Tonikiller10000/W65C02Computer/ComputerPics/20220521_232128.jpg

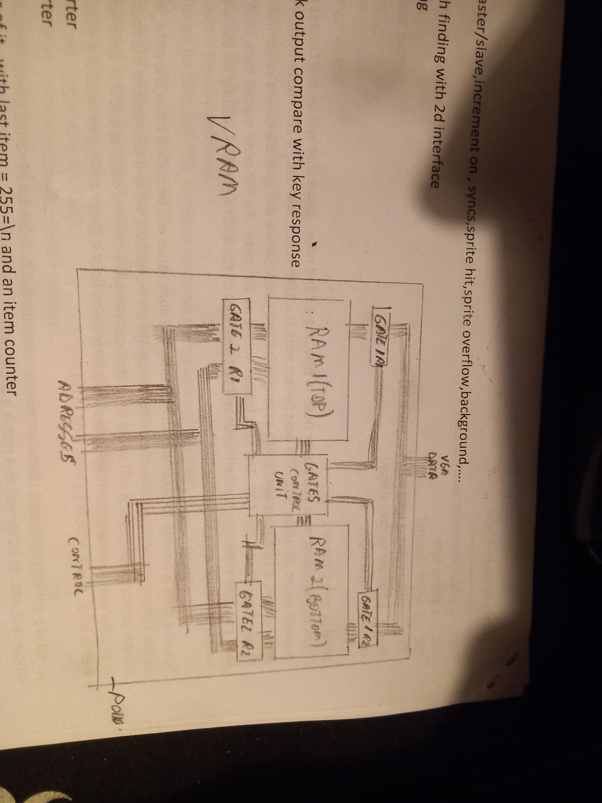
ComputerPics/20220521_232128.jpg
