Tonikiller10000/W65C02Computer/ComputerPics/20220714_215615.jpg

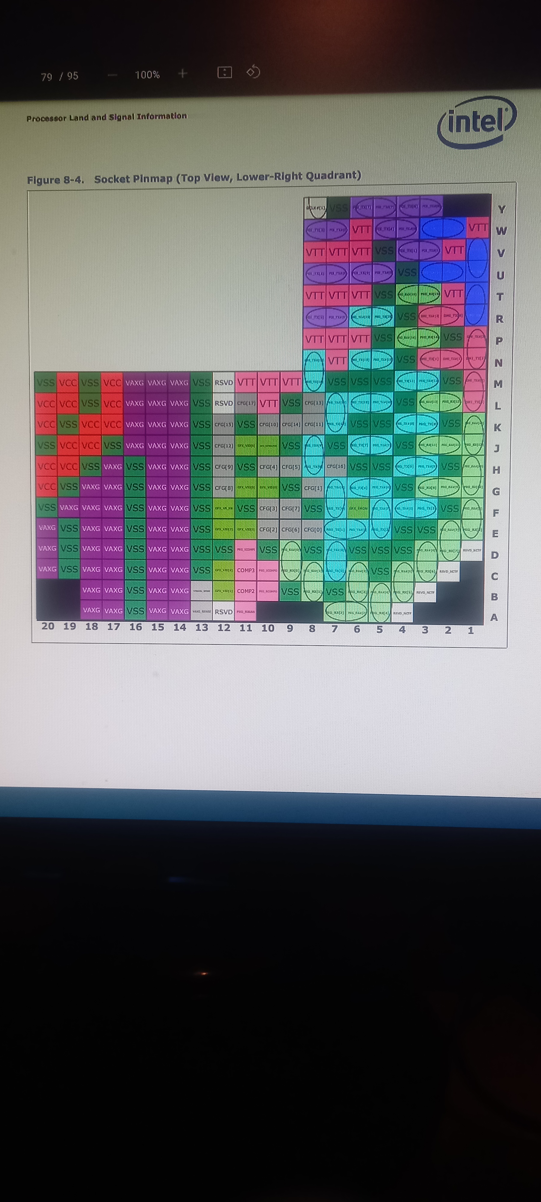
ComputerPics/20220714_215615.jpg
