Tonikiller10000/W65C02Computer/ComputerPics/20230511_115035.jpg

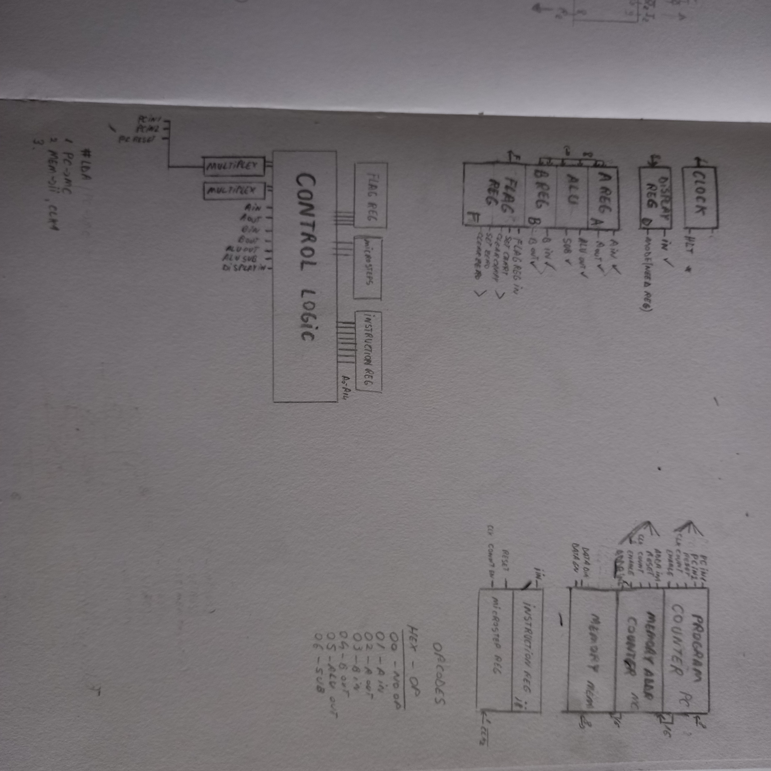
ComputerPics/20230511_115035.jpg
