Tonikiller10000/W65C02Computer/ComputerPics/20230919_042227.jpg

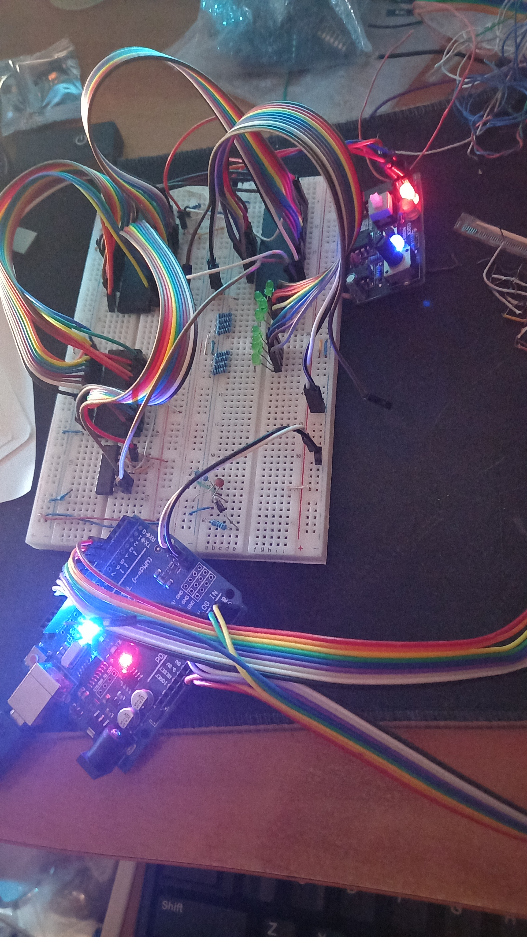
ComputerPics/20230919_042227.jpg
