Tonikiller10000/W65C02Computer/ComputerPics/20240304_115058.jpg

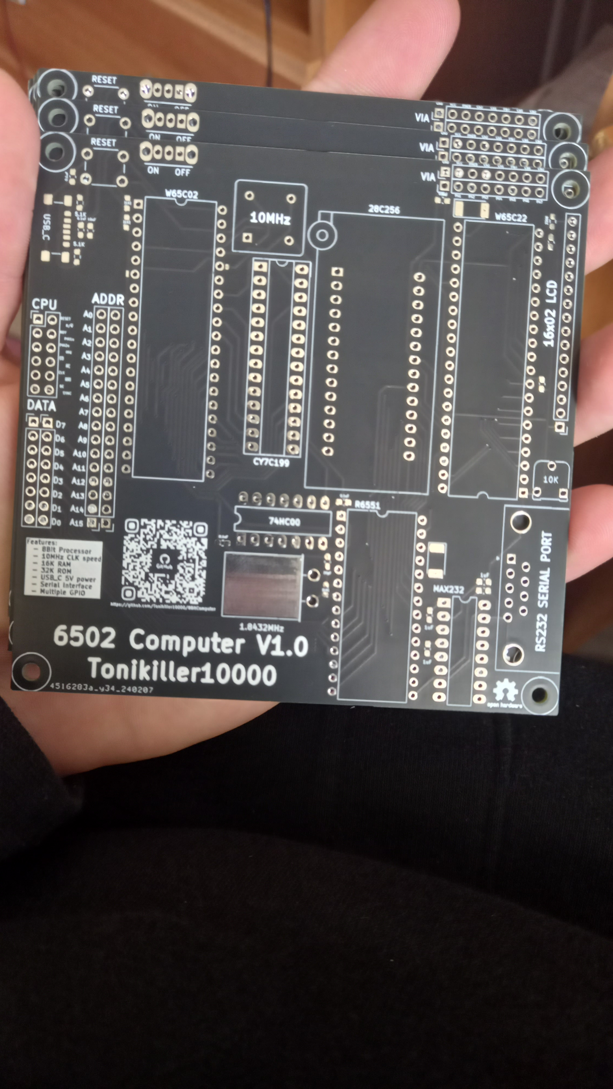
ComputerPics/20240304_115058.jpg
