Tonikiller10000/W65C02Computer/ComputerPics/20240304_115102.jpg

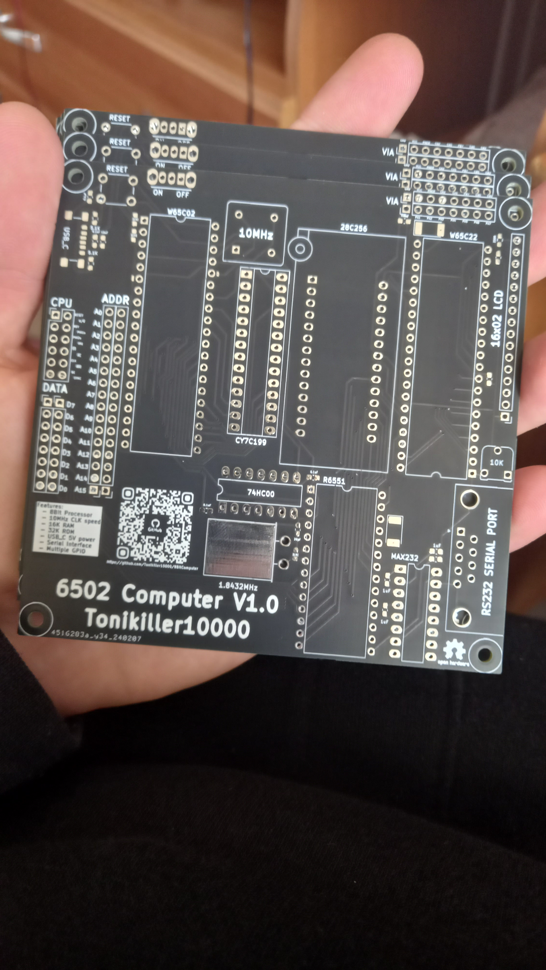
ComputerPics/20240304_115102.jpg
