Tonikiller10000/W65C02Computer/ComputerPics/IMG-20220809-WA0016.jpeg

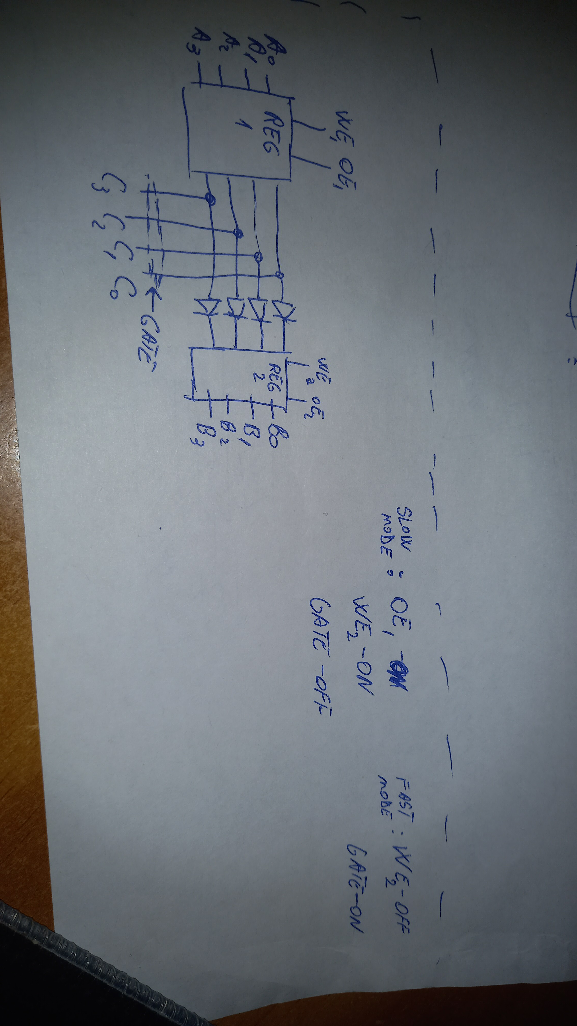
ComputerPics/IMG-20220809-WA0016.jpeg
