Tonikiller10000/W65C02Computer/ComputerPics/IMG-20220811-WA0000.jpeg

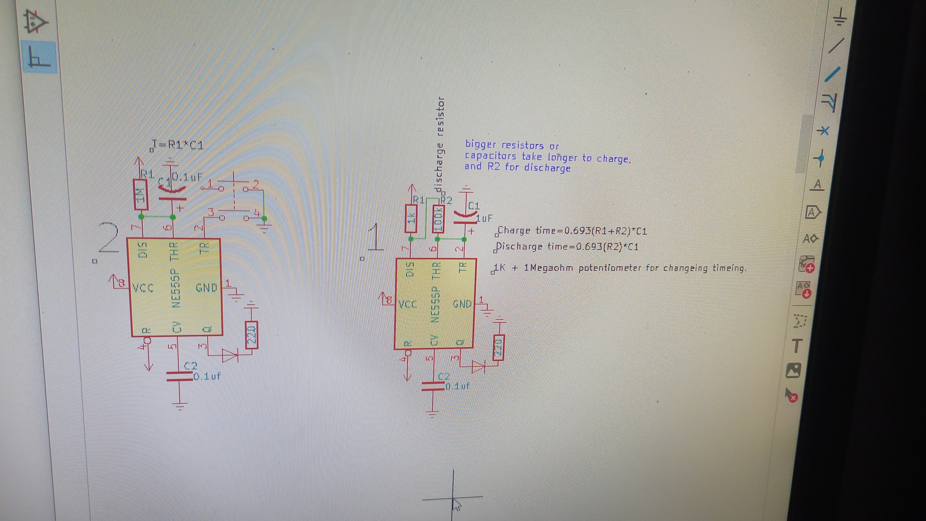
ComputerPics/IMG-20220811-WA0000.jpeg
