Tonikiller10000/W65C02Computer/ComputerPics/IMG-20220811-WA0005.jpeg

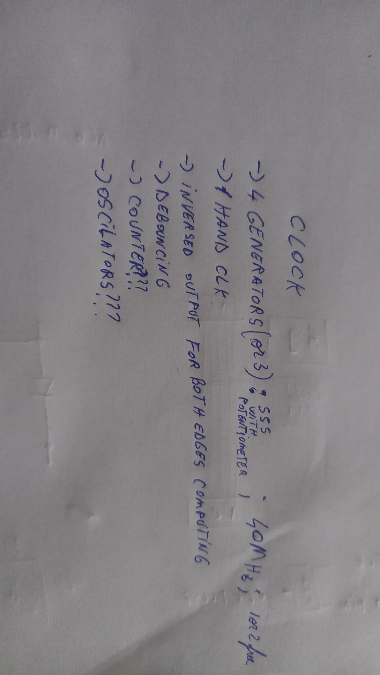
ComputerPics/IMG-20220811-WA0005.jpeg
