Tonikiller10000/W65C02Computer/ComputerPics/IMG-20220814-WA0008.jpeg

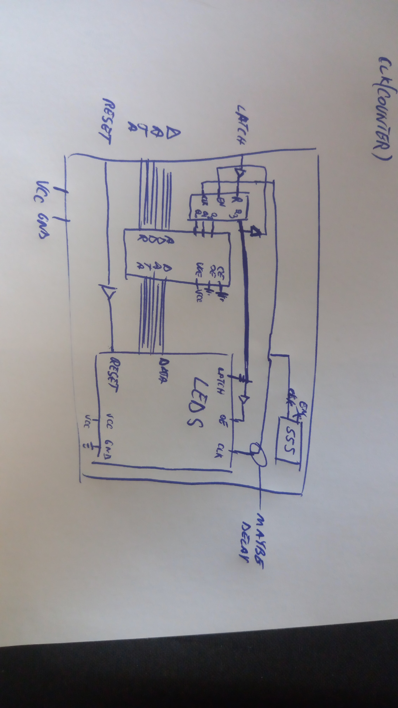
ComputerPics/IMG-20220814-WA0008.jpeg
