Tonikiller10000/W65C02Computer/ComputerPics/Screenshot 2023-10-15 125508.png

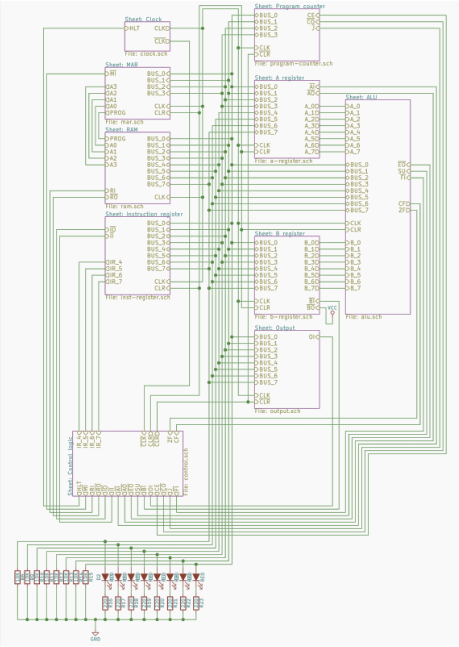
ComputerPics/Screenshot 2023-10-15 125508.png
