Tonikiller10000/W65C02Computer/ComputerPics/Screenshot 2024-01-11 041216.png

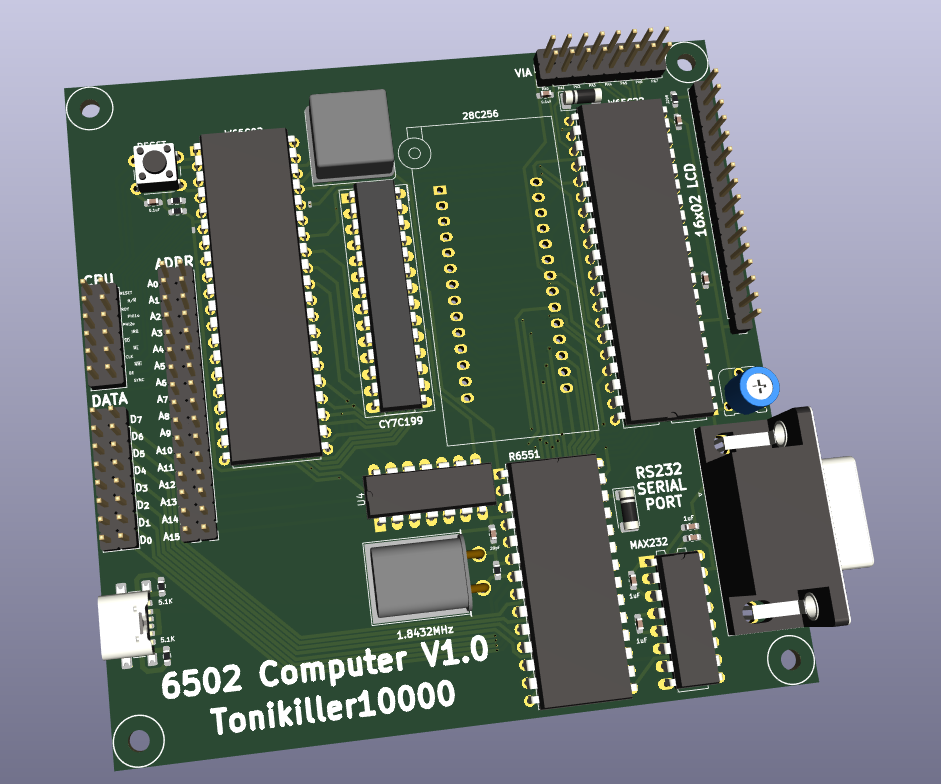
ComputerPics/Screenshot 2024-01-11 041216.png
