Tonikiller10000/W65C02Computer/ComputerPics/Screenshot_20220806-040751_YouTube.jpg

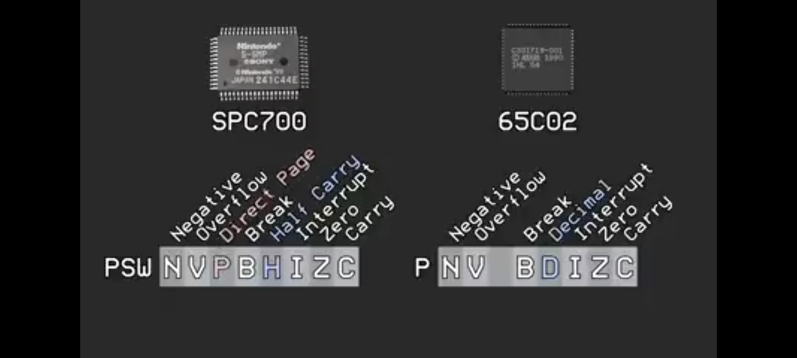
ComputerPics/Screenshot_20220806-040751_YouTube.jpg
