Tonikiller10000/W65C02Computer/ComputerPics/Screenshot_20220821-014721_YouTube.jpg

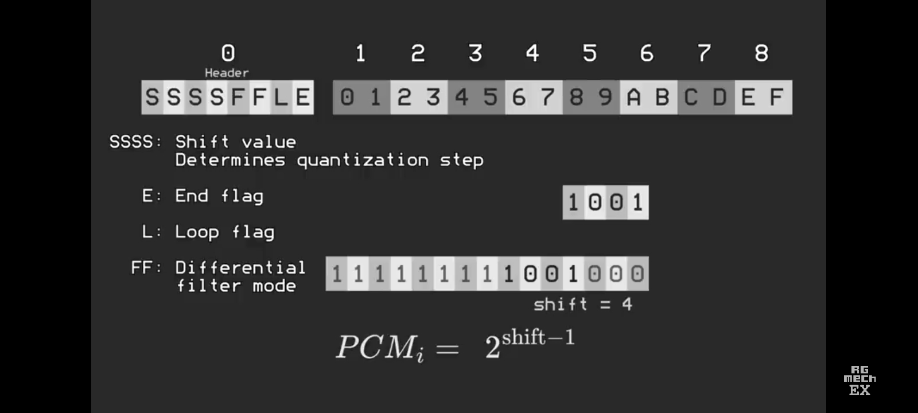
ComputerPics/Screenshot_20220821-014721_YouTube.jpg
