Tonikiller10000/W65C02Computer/ComputerPics/Screenshot_20220821-015238_YouTube.jpg

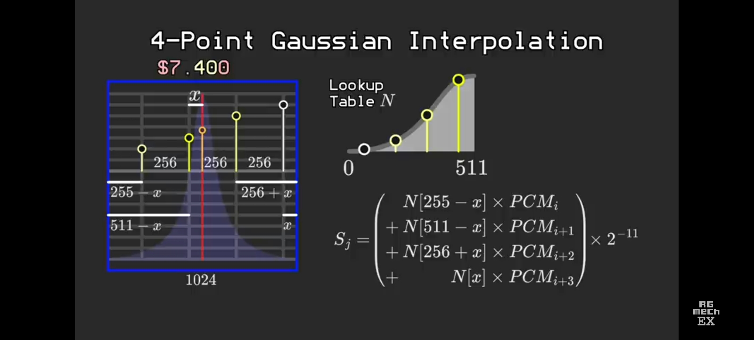
ComputerPics/Screenshot_20220821-015238_YouTube.jpg
