Tonikiller10000/W65C02Computer/ComputerPics/Screenshot_20221124-122945_YouTube.jpg

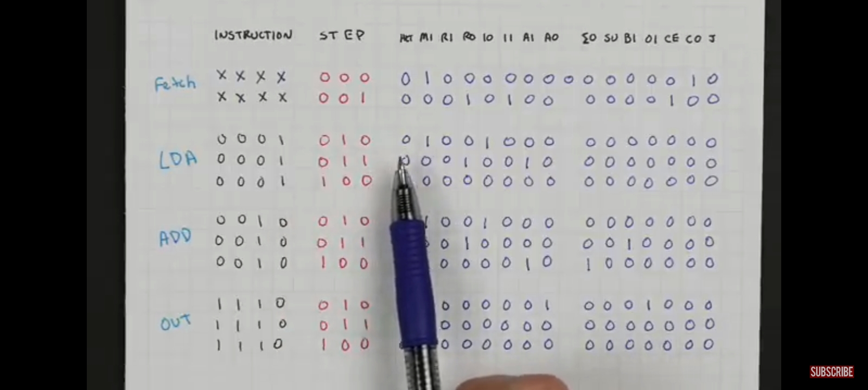
ComputerPics/Screenshot_20221124-122945_YouTube.jpg
