Tonikiller10000/W65C02Computer/ComputerPics/WhatsApp Image 2024-03-29 at 21.50.37 (1).jpeg

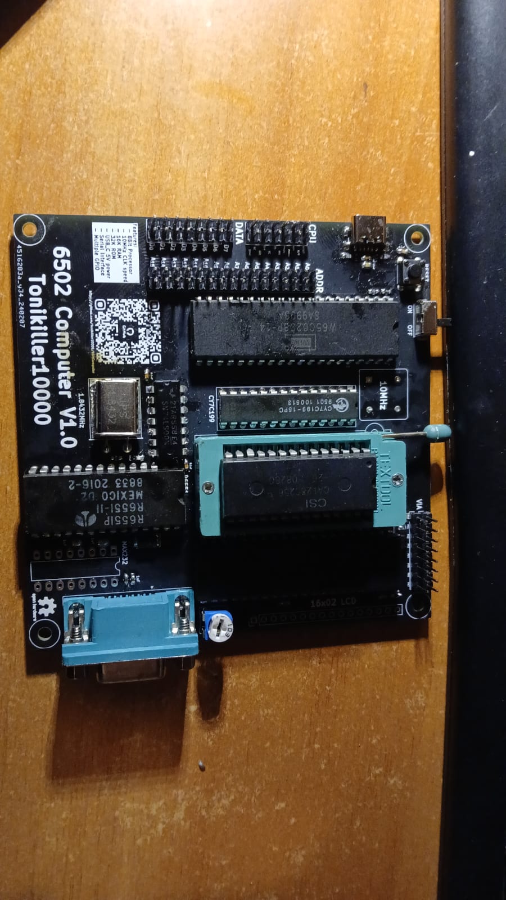
ComputerPics/WhatsApp Image 2024-03-29 at 21.50.37 (1).jpeg
