Tonikiller10000/W65C02Computer/ComputerPics/IMG-20220812-WA0014.jpeg

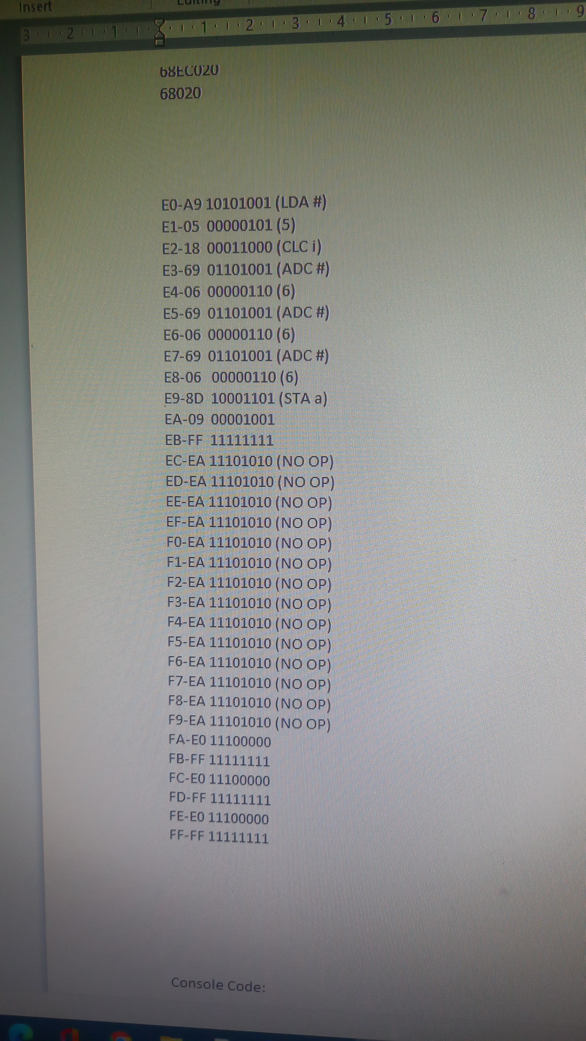
ComputerPics/IMG-20220812-WA0014.jpeg
